chrumck/KnurDash/LTSpice/canON_V2.asc

C1: cap; 2µ
C2: cap; 1µ
C3: cap; 100n
CANbus: voltage; 5V
CANbusLoad: res; 10k
canController: res; 500
canRelay: sw; canRelay
D1: zener; PH_BZX84C3V3
D2: diode; 1N4148
D3: diode; 1N4148
Drelay: diode; 1N4148
Lrelay: ind; 10m
M2: pmos; AONR21305C
M3: nmos; BSC016N03MS
Q1: npn; BC547B
R1: res; 10k
R2: res; 10k
R4: res; 68k
R5: res; 10k
R6: res; 500k
R7: res; 10k
RPI_canOn: voltage; PULSE(0 3.3 1 0.01 0.01 5 20)
RPI_VCC5: voltage; 5V
Rrelay: res; 140
U1: LM311
Named nets: 0
.model canRelay SW(Ron=0.150 Roff=10Meg Vt=4.375 Vh=-0.625)
.tran 20
.include LM311.301
