chrumck/KnurDash/LTSpice/IGN signal in.asc

D1: zener; PH_BZX84C3V3
M1: nmos; BSC016N03MS
R1: res; 10k
R2: res; 100
R3: res; 10k
V1: voltage; 12
V2: voltage; 5
Named nets: 0
.tran 1
