chrumck/KnurDash/LTSpice/PowerOn_V2.asc

12V_VCC: voltage; 12V
C1: cap; 3.3µF
C2: cap; 1µF
D1: zener; TFZV11B
D2: diode; 1N4148
D3: zener; BZX84C10L
GLOBAL_EN_input: res; 10Meg
GLOBAL_EN_pullup: res; 10k
IGN: voltage; PULSE(0 12 1 0.01 0.01 8 20 1)
M1: nmos; BSC016N03MS
Q1: npn; BC547B
R1: res; 10k
R2: res; 10k
R3: res; 47k
R4: res; 10k
R5: res; 47k
R6: res; 10k
R7: res; 10k
RPI_VCC3.3: voltage; 0
RPI_VCC5: voltage; 5V
U1: LM311
Named nets: 0
.tran 30s
.include LM311.301
