chrumck/KnurDash/LTSpice/TransPump.asc

5V: voltage; 5
GPIO: voltage; 0
M1: pmos; AONR21305C
Q1: npn; BC547B
R1: res; 10k
R2: res; 2k
TransPump: res; 100
Named nets: 0
.tran 1
