chrumck/KnurDash/LTSpice/ADCRefCircuit.asc

D1: zener; PH_BZX84C3V3
R1: res; 25
R3: res; 2000
V1: voltage; 5
Named nets: 0
.tran 1
