chrumck/KnurDash/LTSpice/Buzzer.asc

3.3V: voltage; 5
5V: voltage; 5
Buzzer: res; 2.5k
M1: nmos; BSC016N03MS
Named nets: 0
.tran 1
