chrumck/KnurDash/LTSpice/CommonGroundSensorCables.asc

CableHigh1: res; 1
CableHigh2: res; 1
CableLow1: res; 1
Ref2: res; 2000
Ref: res; 2000
Rsensor1: res; 50
Rsensor2: res; 100
V1: voltage; 3.3
Named nets: 0
.tran 1
